vroland/epdiy-hardware/epdiy-v7-raw/components/3d/THD2528-11SD-GF_microSD.step

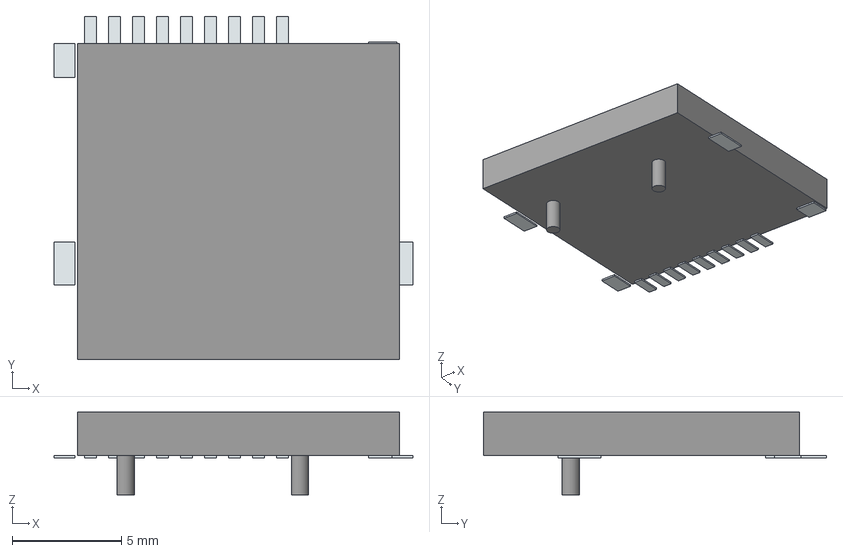
[picture p24: CAD file, 2025-03-17]
epdiy-v7-raw/components/3d/THD2528-11SD-GF_microSD.step
16.5 x 15.7 x 3.80 mm
Pins
Lugs x 2
