vroland/epdiy-hardware/epdiy-v7-raw/components/3d/RV-3032-C7.stp

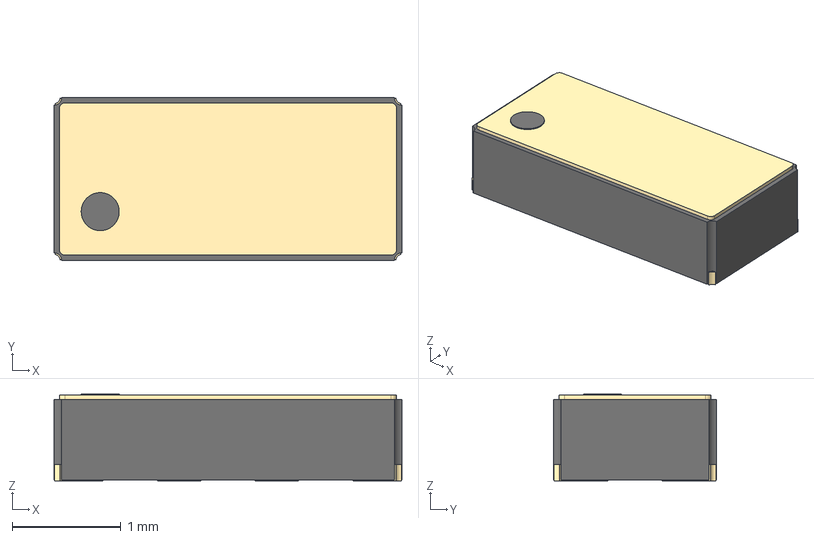
[picture p25: CAD file, 2025-03-17]
epdiy-v7-raw/components/3d/RV-3032-C7.stp
3.20 x 1.50 x 0.8 mm
Rect2
Rect3
Rect4
Rect5
Terminal
