vroland/epdiy-hardware/epdiy-v7-raw/components/3d/xf2m-3315-1a.step

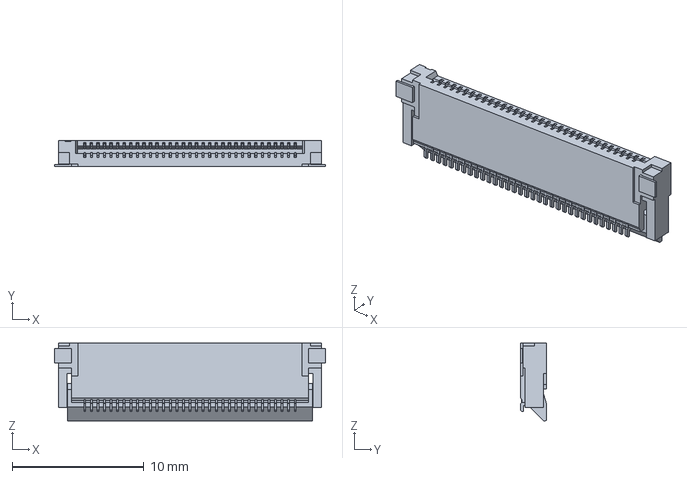
[picture p26: CAD file, 2025-03-17]
epdiy-v7-raw/components/3d/xf2m-3315-1a.step
20.6 x 2.00 x 5.90 mm
