vroland/epdiy-hardware/epdiy-v7-raw/components/3d/S2B-PH-SM4-TB_LF_BatteryJACK.stp

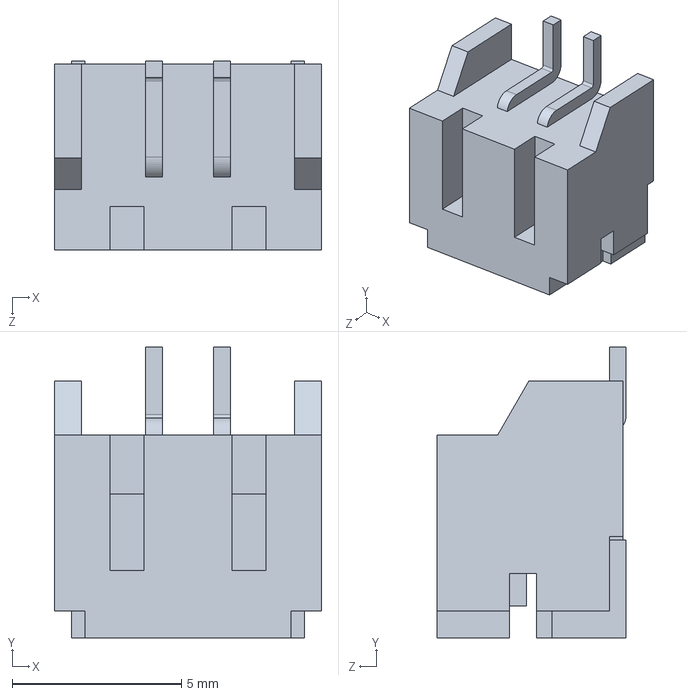
[picture p27: CAD file, 2025-03-17]
epdiy-v7-raw/components/3d/S2B-PH-SM4-TB_LF_BatteryJACK.stp
7.90 x 8.60 x 5.60 mm
