vroland/epdiy-hardware/epdiy-v7-raw/components/3d/X05A20H34G_EPD_connector.step

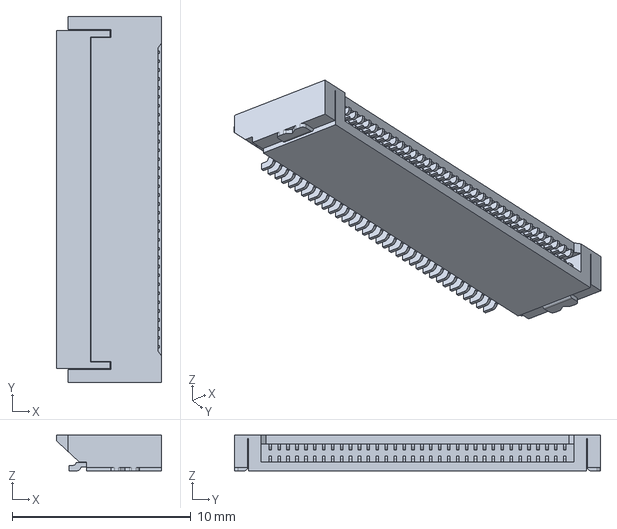
[picture p28: CAD file, 2023-11-06]
epdiy-v7-raw/components/3d/X05A20H34G_EPD_connector.step
5.90 x 20.5 x 2.00 mm
