vroland/epdiy-hardware/epdiy-v7-raw/components/3d/Tactal Switch - SMD (5mmx 5mmx1.5mm).stp

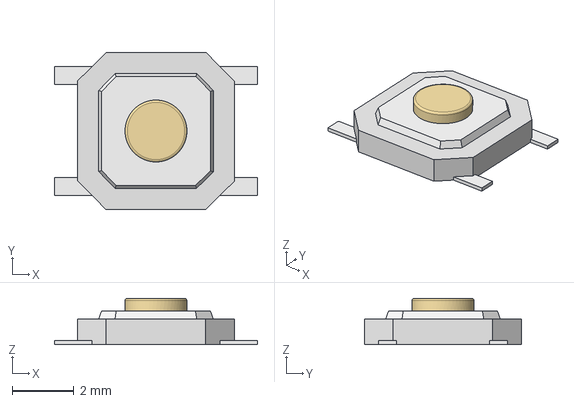
[picture p29: CAD file, 2020-06-02]
epdiy-v7-raw/components/3d/Tactal Switch - SMD (5mmx 5mmx1.5mm).stp
6.58 x 5.10 x 1.50 mm
