vroland/epdiy-hardware/epdiy-v7-raw/components/3d/FH12-33S-0.5SH.step

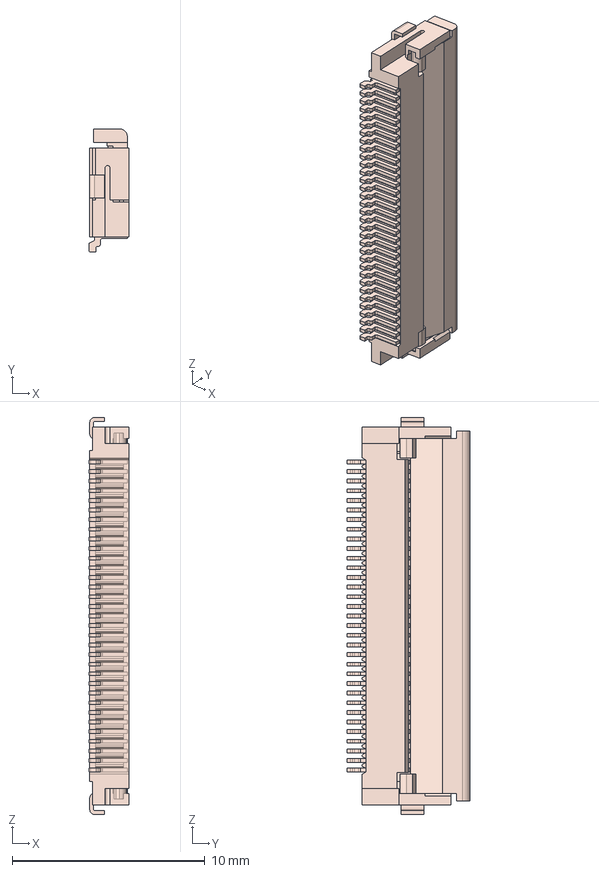
[picture p30: CAD file, 2020-06-02]
epdiy-v7-raw/components/3d/FH12-33S-0.5SH.step
2.10 x 6.40 x 20.6 mm
